gavinbreaux777/Cam_Tracking_Pi/not_code/Images/Physical_System/Belt_Driven_Pan_Table_Img3.jpg

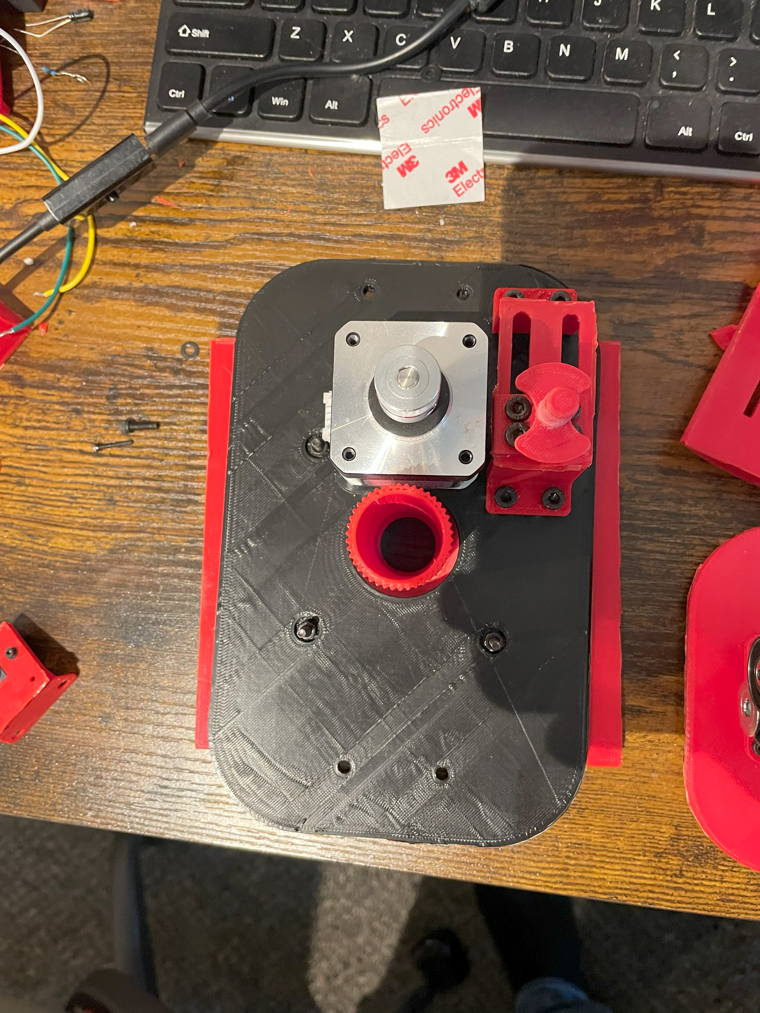
not_code/Images/Physical_System/Belt_Driven_Pan_Table_Img3.jpg
