gavinbreaux777/Cam_Tracking_Pi/not_code/Solidworks/V4_X Motor Tensioner Mount_V4.SLDPRT

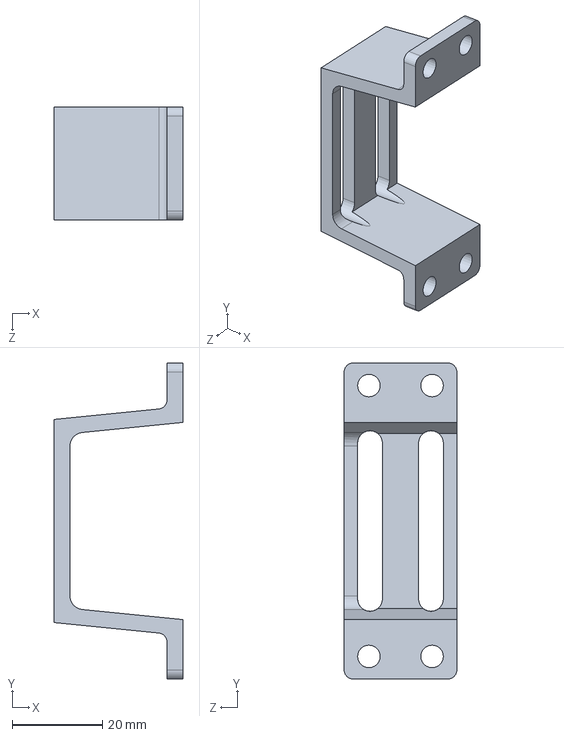
[picture p17: CAD file, 2026-02-15]
not_code/Solidworks/V4_X Motor Tensioner Mount_V4.SLDPRT
28.5 x 70.0 x 25.0 mm
