gavinbreaux777/Cam_Tracking_Pi/not_code/Solidworks/V4_SD Card Slot, RPi4ModelB.SLDPRT

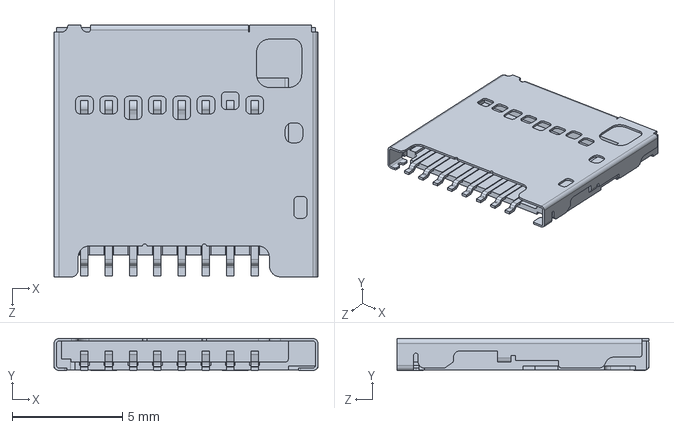
[picture p18: CAD file, 2026-02-15]
not_code/Solidworks/V4_SD Card Slot, RPi4ModelB.SLDPRT
11.9 x 1.45 x 11.4 mm
