gavinbreaux777/Cam_Tracking_Pi/not_code/Solidworks/V4_Cam case V4.SLDPRT

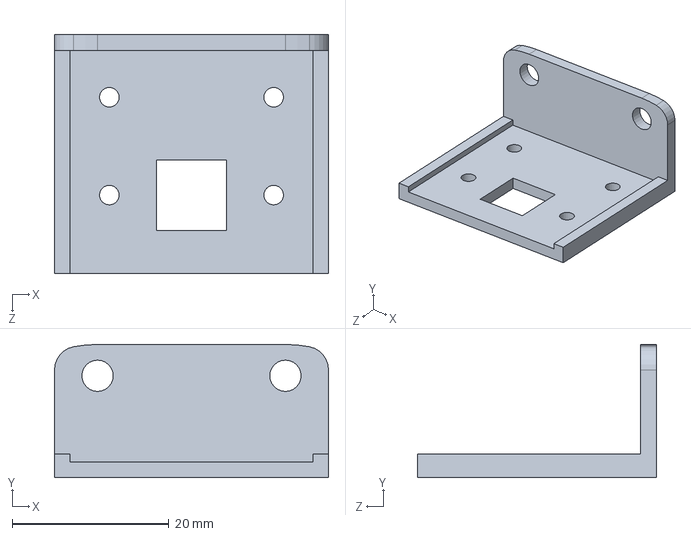
[picture p19: CAD file, 2026-02-15]
not_code/Solidworks/V4_Cam case V4.SLDPRT
35.0 x 17.0 x 30.5 mm
