gavinbreaux777/Cam_Tracking_Pi/not_code/Solidworks/V4_X Motor Tensioner Rod Cap.SLDPRT

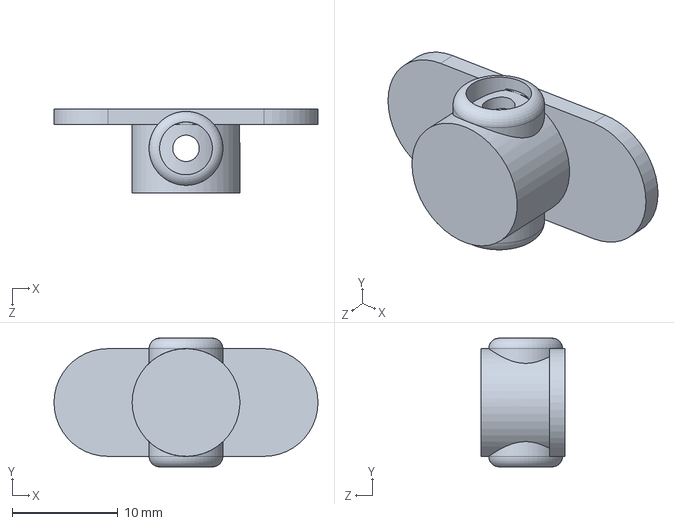
[picture p20: CAD file, 2026-02-15]
not_code/Solidworks/V4_X Motor Tensioner Rod Cap.SLDPRT
25.0 x 12.2 x 8.00 mm
