gavinbreaux777/Cam_Tracking_Pi/not_code/Solidworks/V4_Servo gate attachment.SLDPRT

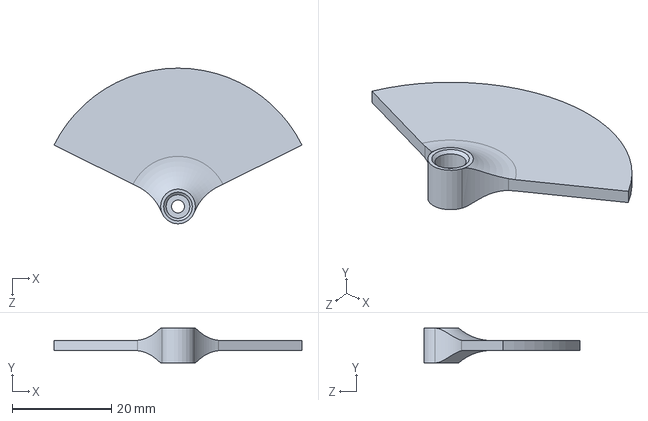
[picture p21: CAD file, 2026-02-15]
not_code/Solidworks/V4_Servo gate attachment.SLDPRT
50.0 x 7.00 x 31.4 mm
