gavinbreaux777/Cam_Tracking_Pi/not_code/Solidworks/V4_Direct Motor Mount V6_V3.SLDPRT

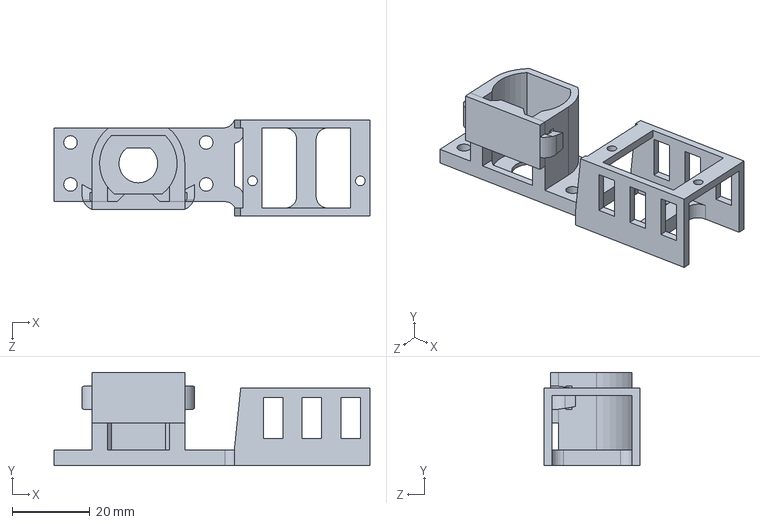
[picture p22: CAD file, 2026-02-15]
not_code/Solidworks/V4_Direct Motor Mount V6_V3.SLDPRT
81.5 x 24.0 x 24.7 mm
