gavinbreaux777/Cam_Tracking_Pi/not_code/Solidworks/V4_Female USB Type C Connector, RPi4ModelB.SLDPRT

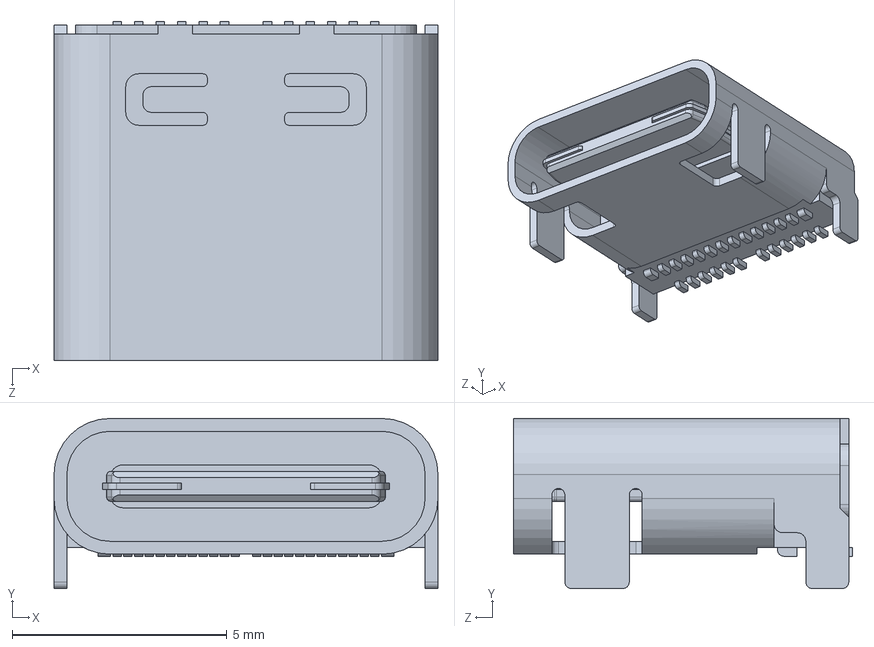
[picture p23: CAD file, 2026-02-15]
not_code/Solidworks/V4_Female USB Type C Connector, RPi4ModelB.SLDPRT
8.94 x 3.96 x 7.90 mm
