gavinbreaux777/Cam_Tracking_Pi/not_code/Solidworks/V4_Base_V3.SLDPRT

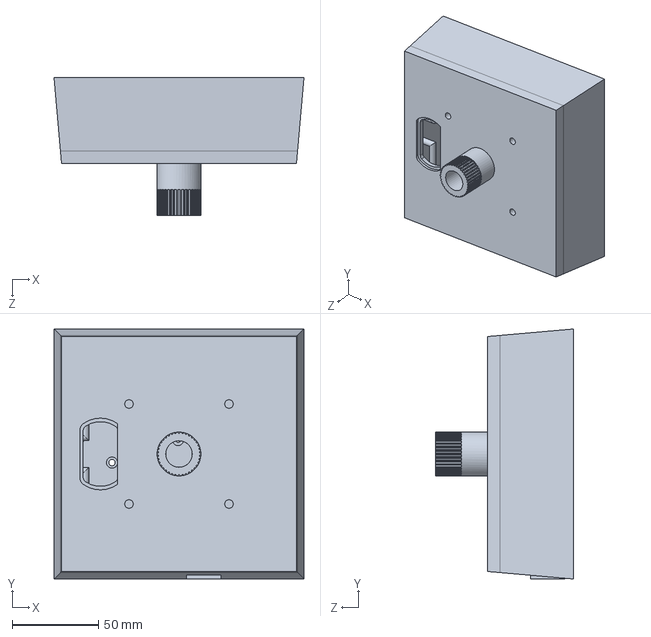
[picture p24: CAD file, 2026-02-15]
not_code/Solidworks/V4_Base_V3.SLDPRT
145.0 x 145.0 x 80.0 mm
