gavinbreaux777/Cam_Tracking_Pi/not_code/Solidworks/V4_Y Motor Tensioner Rod_V3.SLDPRT

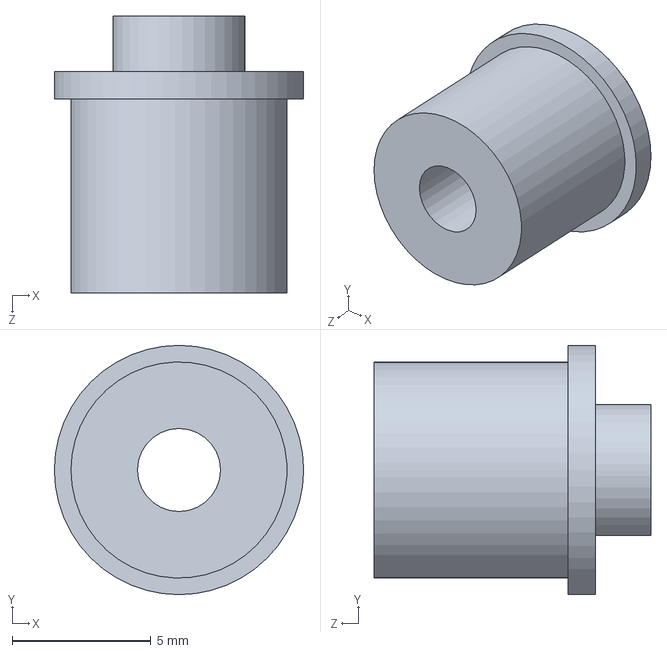
[picture p25: CAD file, 2026-02-15]
not_code/Solidworks/V4_Y Motor Tensioner Rod_V3.SLDPRT
9.00 x 9.00 x 10.0 mm
