gavinbreaux777/Cam_Tracking_Pi/not_code/Solidworks/V4_PCB, RPi4ModelB.SLDPRT

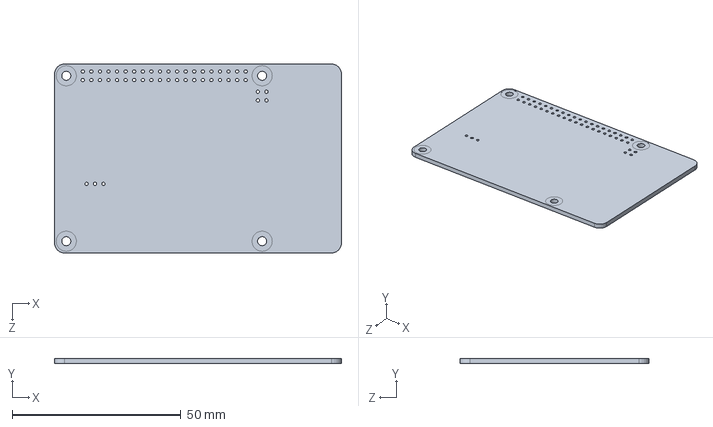
[picture p26: CAD file, 2026-02-15]
not_code/Solidworks/V4_PCB, RPi4ModelB.SLDPRT
85.0 x 1.60 x 56.0 mm
