gavinbreaux777/Cam_Tracking_Pi/not_code/Solidworks/V4_Gigabit Ethernet Port, RPi4ModelB.SLDPRT

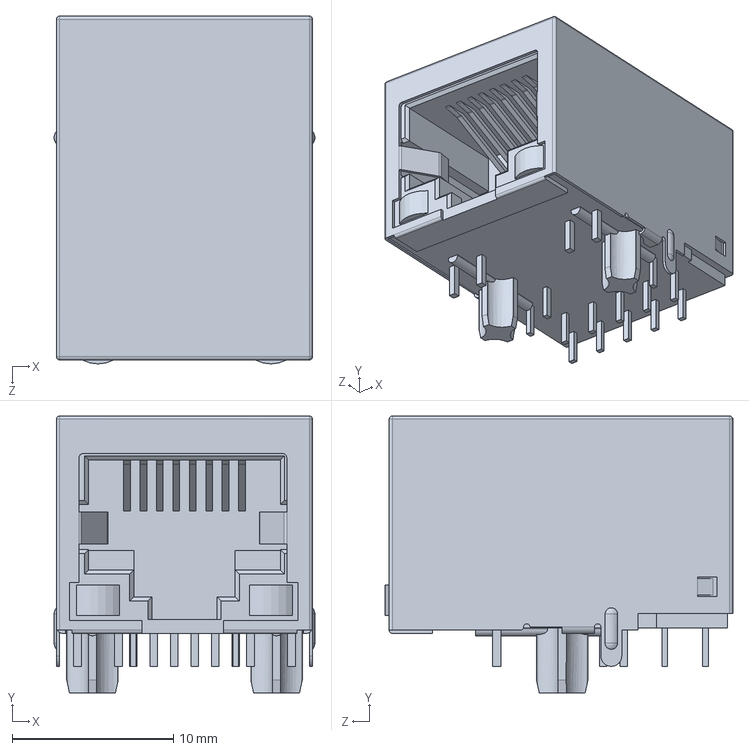
[picture p27: CAD file, 2026-02-15]
not_code/Solidworks/V4_Gigabit Ethernet Port, RPi4ModelB.SLDPRT
16.2 x 17.2 x 21.6 mm
