gavinbreaux777/Cam_Tracking_Pi/not_code/Solidworks/V4_Display Connector, RPi4ModelB.SLDPRT

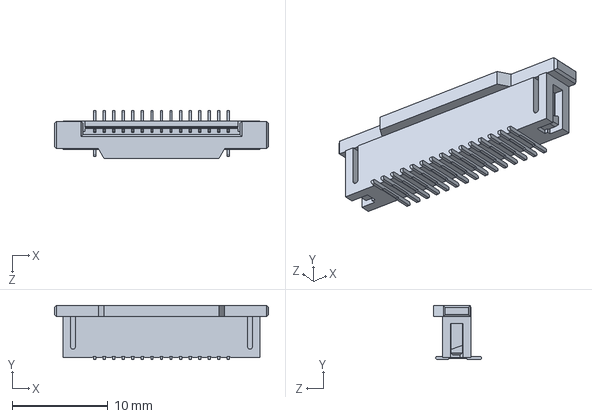
[picture p28: CAD file, 2026-02-15]
not_code/Solidworks/V4_Display Connector, RPi4ModelB.SLDPRT
22.4 x 5.68 x 5.07 mm
