gavinbreaux777/Cam_Tracking_Pi/not_code/Solidworks/V4 X Motor Upside Down Mount_1.SLDPRT

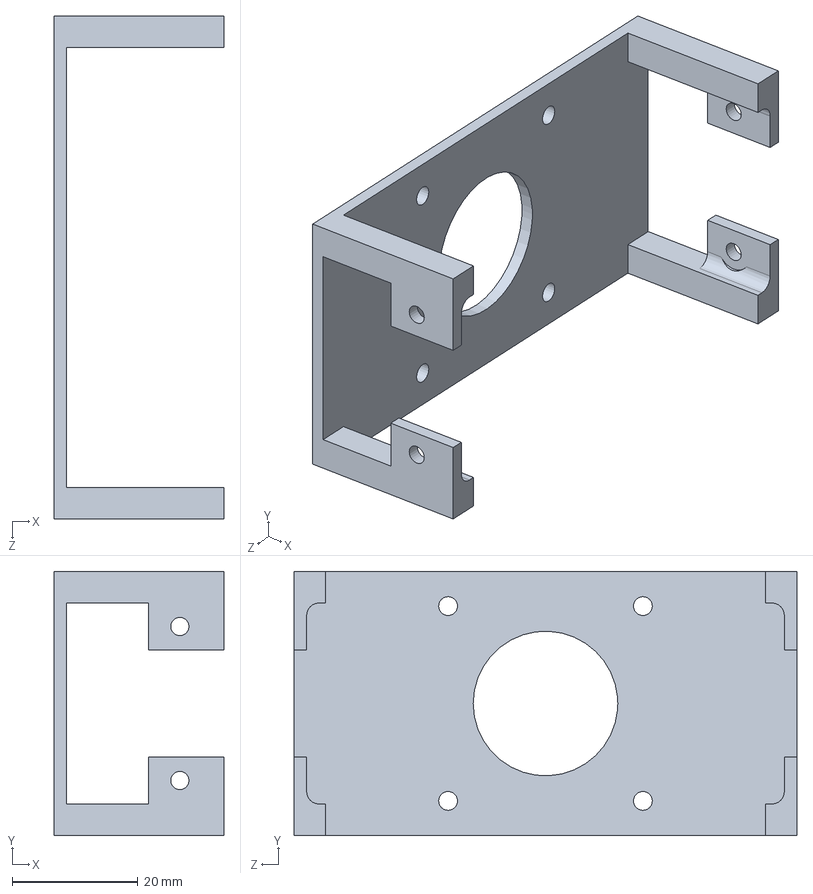
[picture p29: CAD file, 2026-02-15]
not_code/Solidworks/V4 X Motor Upside Down Mount_1.SLDPRT
27.0 x 42.0 x 80.0 mm
