gavinbreaux777/Cam_Tracking_Pi/not_code/Solidworks/V4_Ball Chute V3_V3.SLDPRT

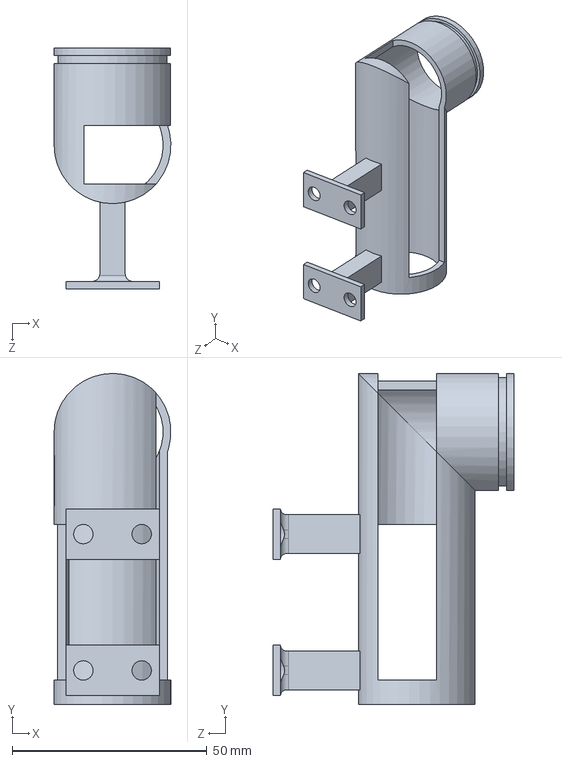
[picture p30: CAD file, 2026-02-15]
not_code/Solidworks/V4_Ball Chute V3_V3.SLDPRT
30.0 x 85.0 x 62.0 mm
