gavinbreaux777/Cam_Tracking_Pi/not_code/Solidworks/V4_Bearing Holder_1.SLDPRT

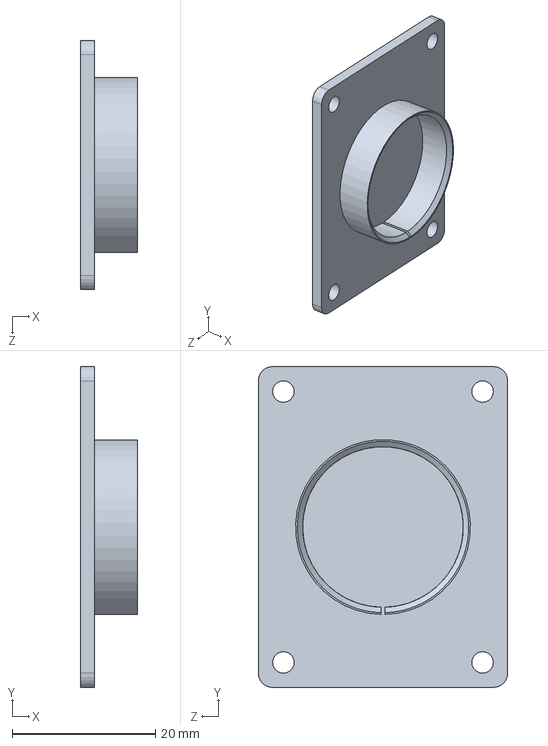
[picture p31: CAD file, 2026-02-15]
not_code/Solidworks/V4_Bearing Holder_1.SLDPRT
8.00 x 44.8 x 34.8 mm
