gavinbreaux777/Cam_Tracking_Pi/not_code/Solidworks/V4_2X USB3.0 PORTS, RPi4ModelB.SLDPRT

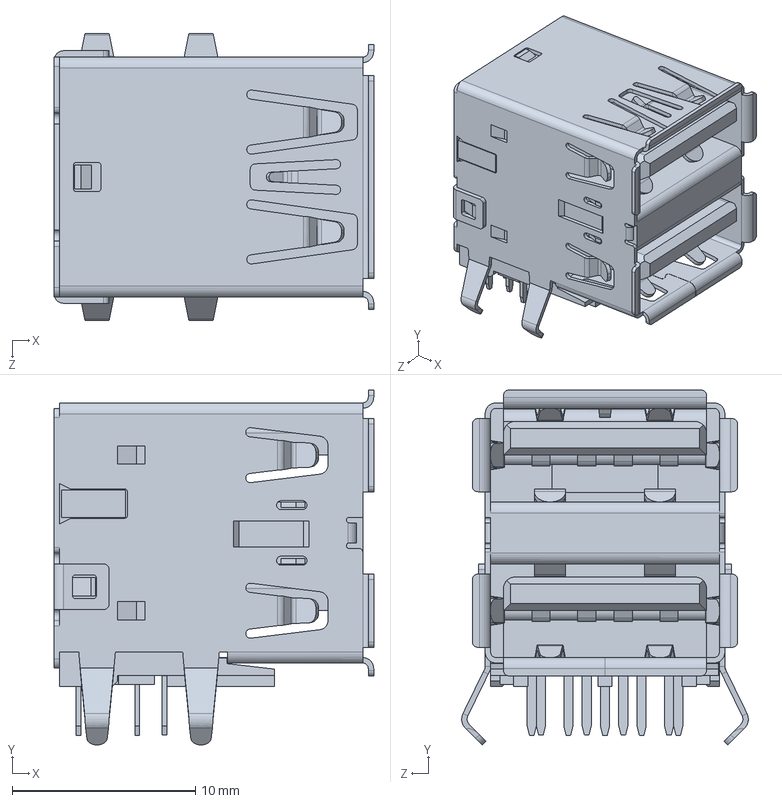
[picture p32: CAD file, 2026-02-15]
not_code/Solidworks/V4_2X USB3.0 PORTS, RPi4ModelB.SLDPRT
17.5 x 19.4 x 15.7 mm
