gavinbreaux777/Cam_Tracking_Pi/not_code/Solidworks/V4_Y Motor Shaft Gear Parametric.SLDPRT

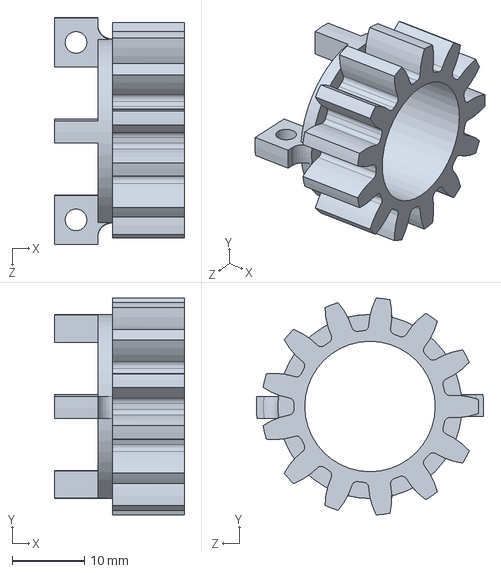
[picture p33: CAD file, 2026-02-15]
not_code/Solidworks/V4_Y Motor Shaft Gear Parametric.SLDPRT
18.0 x 30.0 x 31.4 mm
