gavinbreaux777/Cam_Tracking_Pi/not_code/Solidworks/V4_Half Lazy Susan_V3.SLDPRT

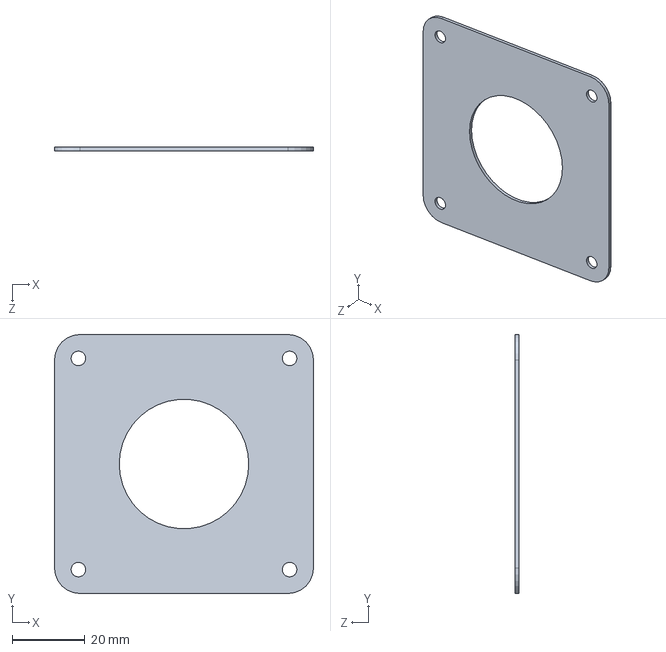
[picture p34: CAD file, 2026-02-15]
not_code/Solidworks/V4_Half Lazy Susan_V3.SLDPRT
71.1 x 71.1 x 1.00 mm
