gavinbreaux777/Cam_Tracking_Pi/not_code/Solidworks/V4_Female Micro HDMI Connector, RPi4ModelB.SLDPRT

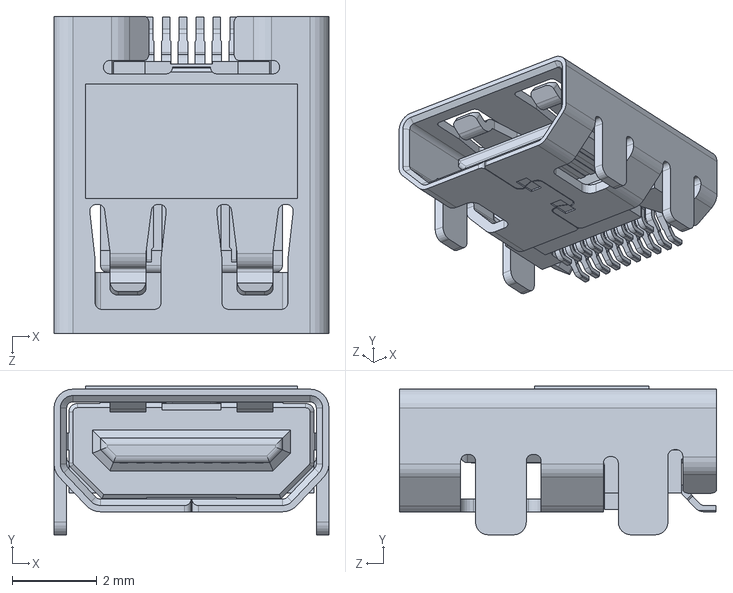
[picture p35: CAD file, 2026-02-15]
not_code/Solidworks/V4_Female Micro HDMI Connector, RPi4ModelB.SLDPRT
6.50 x 3.52 x 7.50 mm
