gavinbreaux777/Cam_Tracking_Pi/not_code/Solidworks/V4_Y Motor Shaft Gear Try 2.SLDPRT

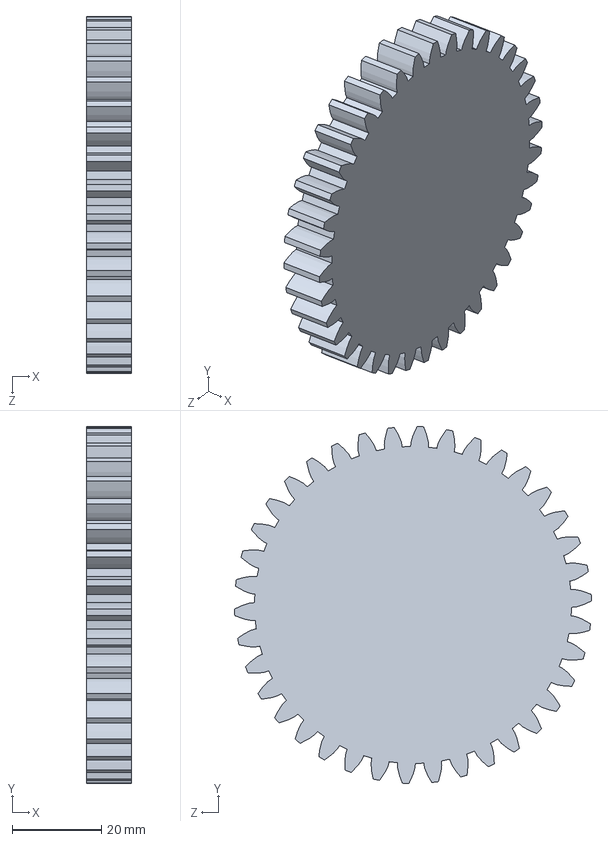
[picture p36: CAD file, 2026-02-15]
not_code/Solidworks/V4_Y Motor Shaft Gear Try 2.SLDPRT
10.0 x 80.0 x 80.0 mm
