gavinbreaux777/Cam_Tracking_Pi/not_code/Solidworks/V4_91D77 D9WHV 778K, 4 GB LPDDR4 SDRAM, RPi4ModelB.SLDPRT

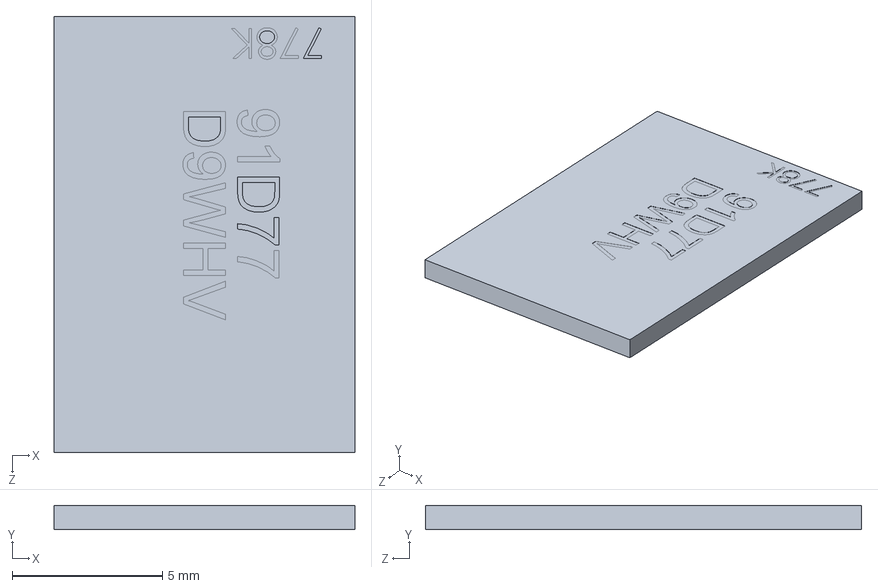
[picture p37: CAD file, 2026-02-15]
not_code/Solidworks/V4_91D77 D9WHV 778K, 4 GB LPDDR4 SDRAM, RPi4ModelB.SLDPRT
10.0 x 0.8 x 14.5 mm
