gavinbreaux777/Cam_Tracking_Pi/not_code/Solidworks/V4_Bearing_608_V3.SLDPRT

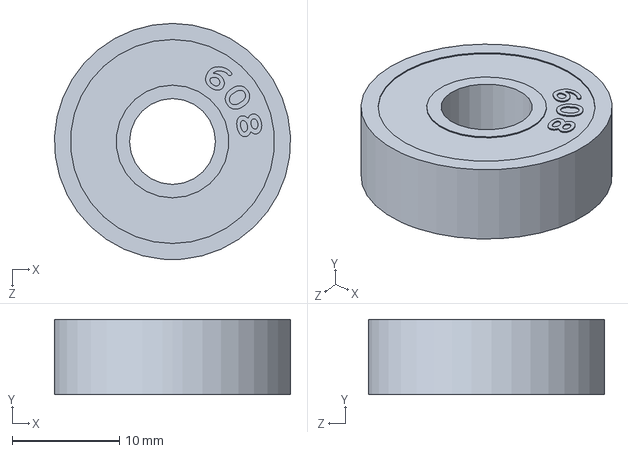
[picture p38: CAD file, 2026-02-15]
not_code/Solidworks/V4_Bearing_608_V3.SLDPRT
22.0 x 7.00 x 22.0 mm
