gavinbreaux777/Cam_Tracking_Pi/not_code/Solidworks/V4_2.54 mm DUPONT MALE PIN HEADER, IO, 2X20, RPi4ModelB.SLDPRT

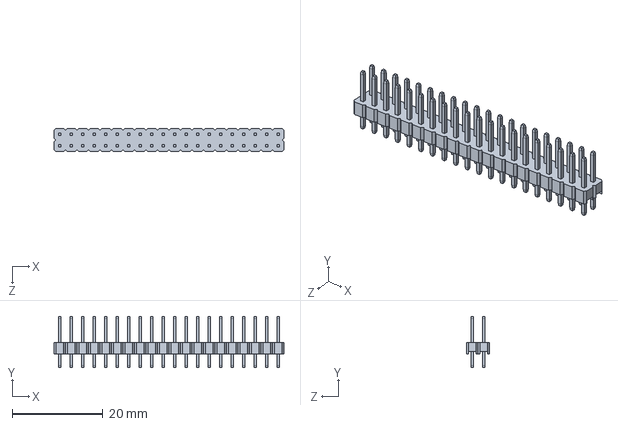
[picture p39: CAD file, 2026-02-15]
not_code/Solidworks/V4_2.54 mm DUPONT MALE PIN HEADER, IO, 2X20, RPi4ModelB.SLDPRT
50.8 x 11.3 x 5.08 mm
