gavinbreaux777/Cam_Tracking_Pi/not_code/Solidworks/V4_Cypress CYW43455 Wireless Module Cover, RPi4ModelB.SLDPRT

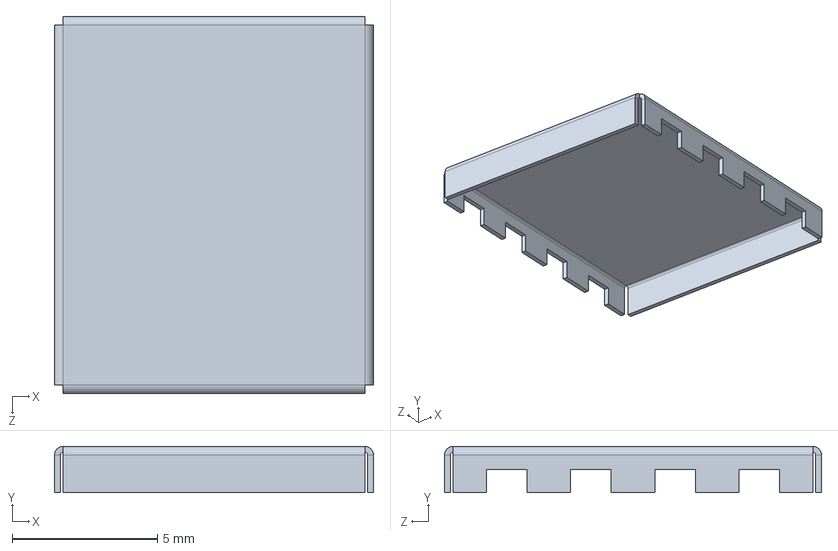
[picture p40: CAD file, 2026-02-15]
not_code/Solidworks/V4_Cypress CYW43455 Wireless Module Cover, RPi4ModelB.SLDPRT
11.0 x 1.60 x 13.0 mm
