gavinbreaux777/Cam_Tracking_Pi/not_code/Solidworks/V4_2X USB2.0 PORTS, RPi4ModelB.SLDPRT

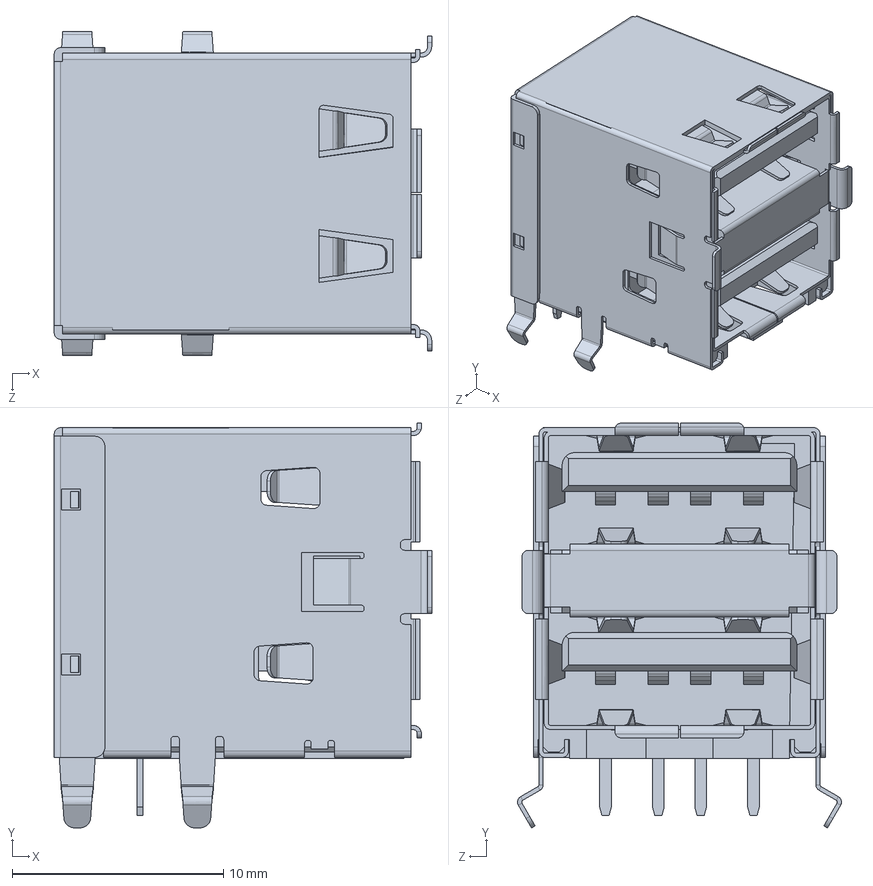
[picture p41: CAD file, 2026-02-15]
not_code/Solidworks/V4_2X USB2.0 PORTS, RPi4ModelB.SLDPRT
17.9 x 19.2 x 15.3 mm
