gavinbreaux777/Cam_Tracking_Pi/not_code/Solidworks/V4_MxL7704 Universal PMIC, RPi4ModelB.SLDPRT

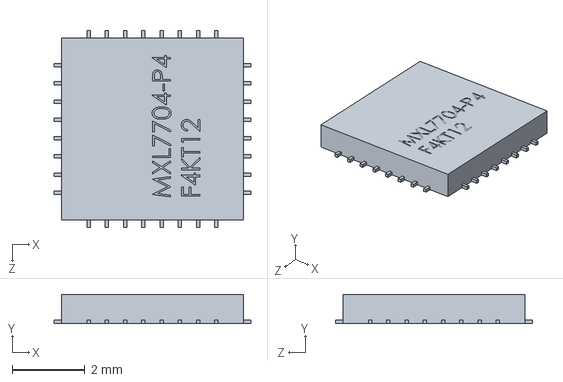
[picture p42: CAD file, 2026-02-15]
not_code/Solidworks/V4_MxL7704 Universal PMIC, RPi4ModelB.SLDPRT
5.40 x 0.8 x 5.40 mm
