gavinbreaux777/Cam_Tracking_Pi/not_code/Solidworks/V4_2.54 mm DUPONT MALE PIN HEADER, POE, 2X2, RPi4ModelB.SLDPRT

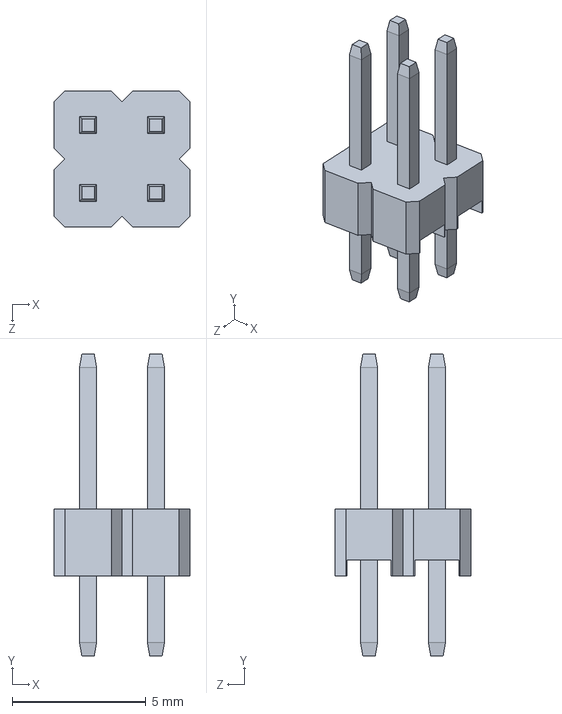
[picture p43: CAD file, 2026-02-15]
not_code/Solidworks/V4_2.54 mm DUPONT MALE PIN HEADER, POE, 2X2, RPi4ModelB.SLDPRT
5.08 x 11.3 x 5.08 mm
