gavinbreaux777/Cam_Tracking_Pi/not_code/Solidworks/V4_Raspberry Pi  Camera.SLDPRT

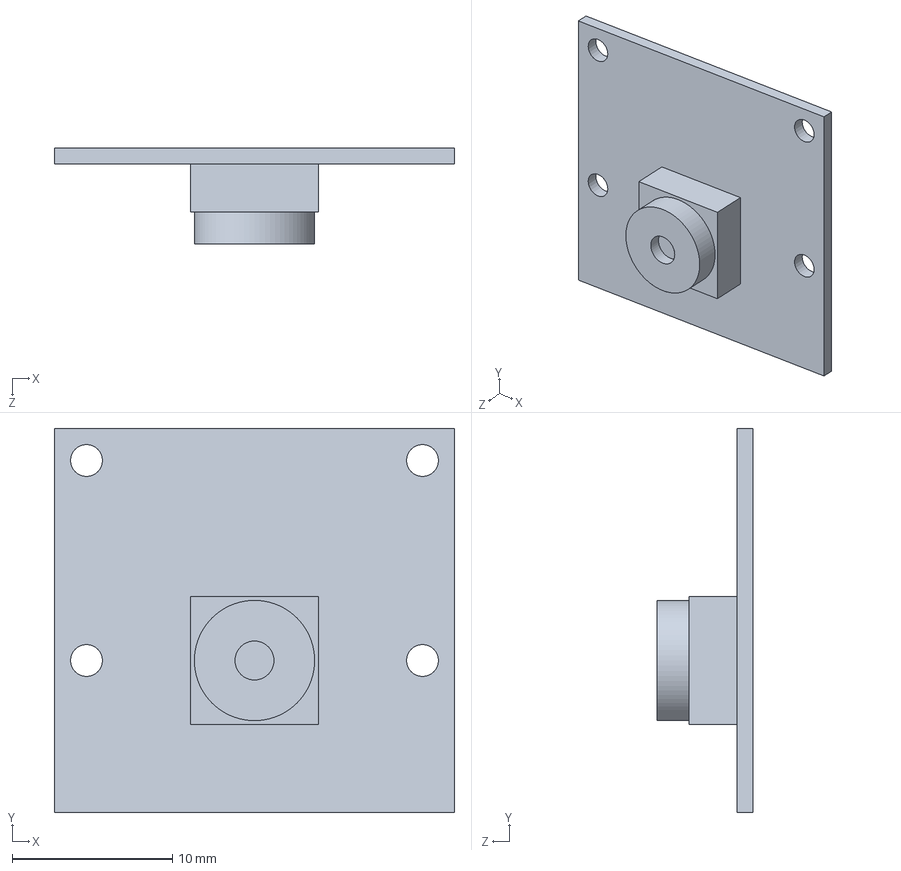
[picture p44: CAD file, 2026-02-15]
not_code/Solidworks/V4_Raspberry Pi Camera.SLDPRT
25.0 x 24.0 x 6.00 mm
