gavinbreaux777/Cam_Tracking_Pi/not_code/Solidworks/V4_Y Motor Shaft Gear Try 3.SLDPRT

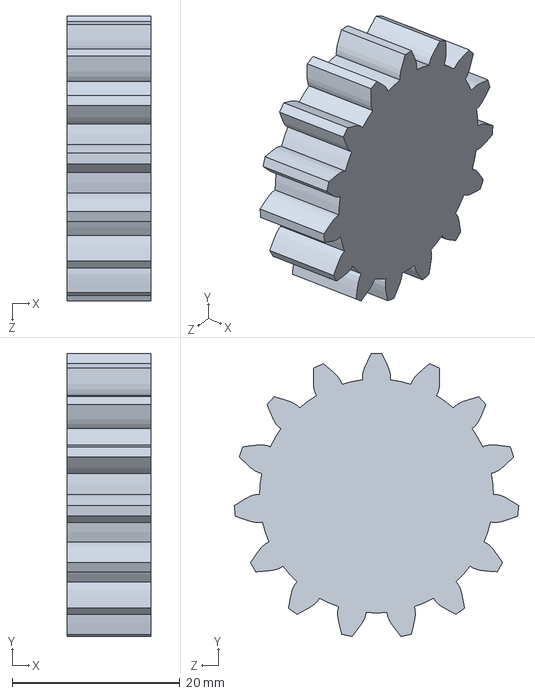
[picture p45: CAD file, 2026-02-15]
not_code/Solidworks/V4_Y Motor Shaft Gear Try 3.SLDPRT
10.0 x 33.7 x 33.9 mm
