gavinbreaux777/Cam_Tracking_Pi/not_code/Solidworks/V4_X Motor Tensioner Rod_V5.SLDPRT

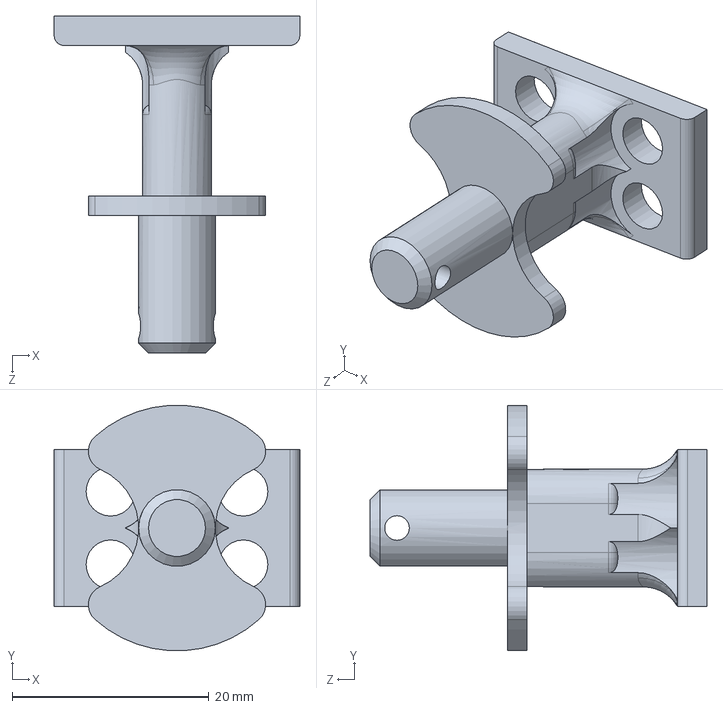
[picture p46: CAD file, 2026-02-15]
not_code/Solidworks/V4_X Motor Tensioner Rod_V5.SLDPRT
25.0 x 24.9 x 34.3 mm
