gavinbreaux777/Cam_Tracking_Pi/not_code/Solidworks/V4_Microphone Plug, RPi4ModelB.SLDPRT

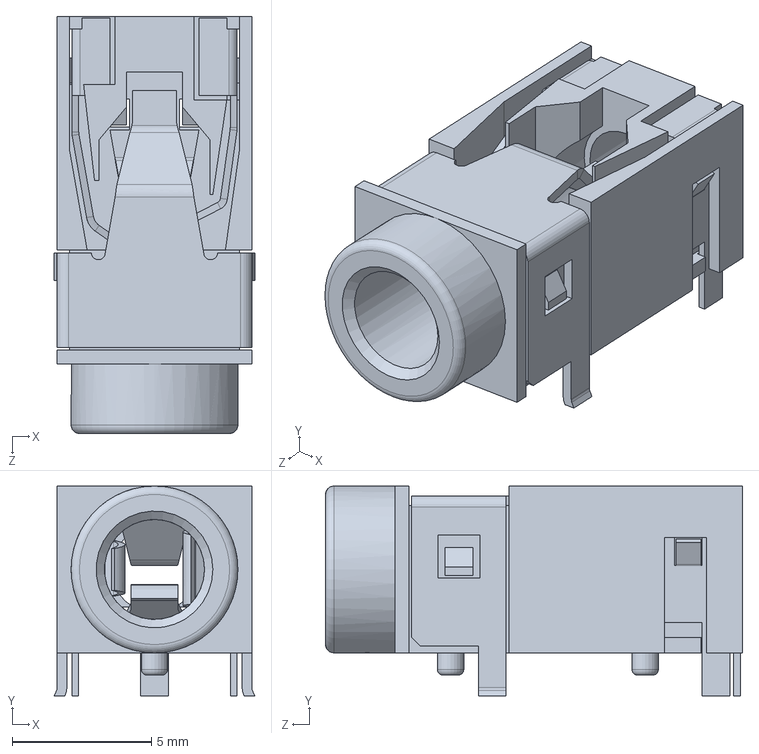
[picture p47: CAD file, 2026-02-15]
not_code/Solidworks/V4_Microphone Plug, RPi4ModelB.SLDPRT
7.23 x 7.55 x 15.0 mm
