gavinbreaux777/Cam_Tracking_Pi/not_code/Solidworks/V4_Base_V4.SLDPRT

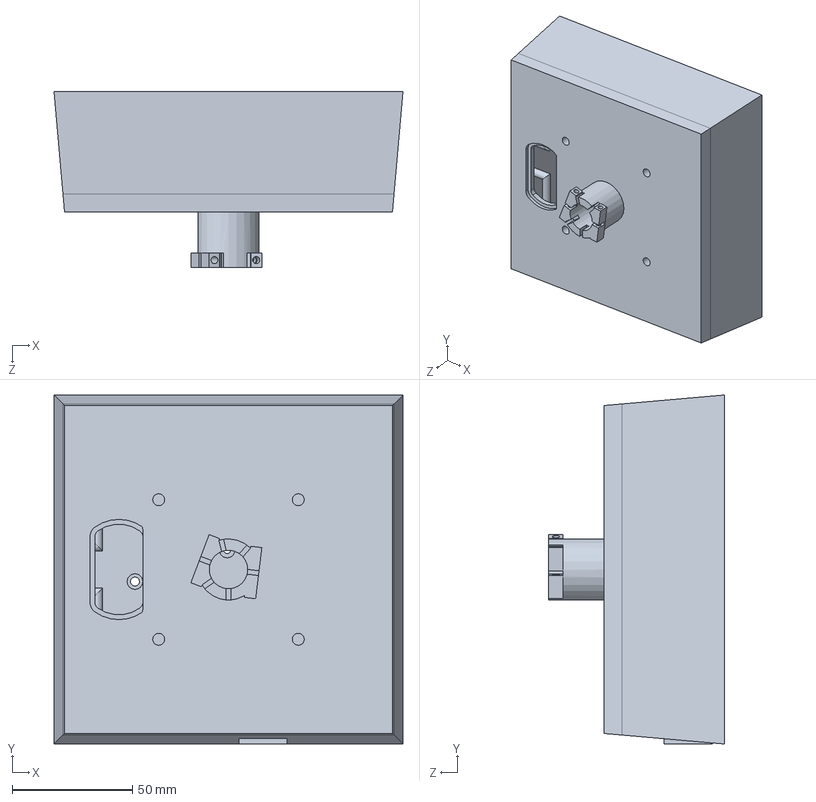
[picture p48: CAD file, 2026-02-15]
not_code/Solidworks/V4_Base_V4.SLDPRT
145.0 x 145.0 x 73.0 mm
