gavinbreaux777/Cam_Tracking_Pi/not_code/Solidworks/V4_Base_V5SLDPRT.SLDPRT

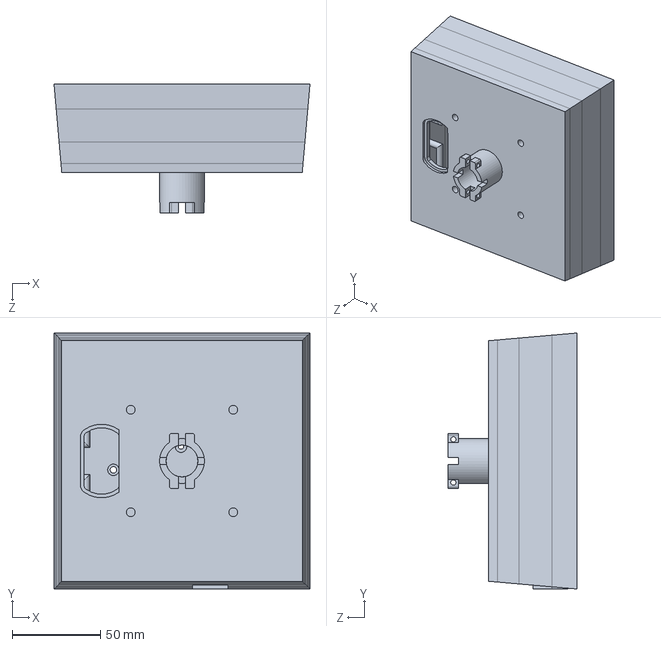
[picture p49: CAD file, 2026-02-15]
not_code/Solidworks/V4_Base_V5SLDPRT.SLDPRT
145.0 x 145.0 x 73.0 mm
