gavinbreaux777/Cam_Tracking_Pi/not_code/Solidworks/V4_Tilt Table Riser_Adjustable_Bearing_1.SLDPRT

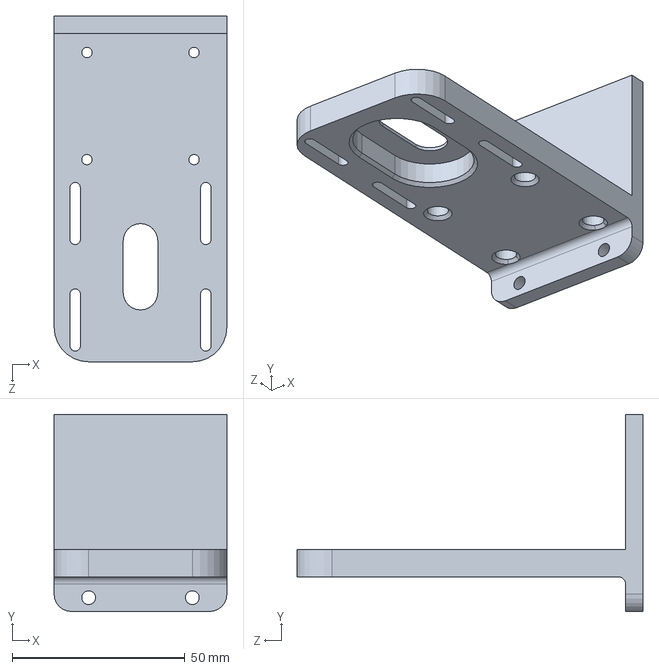
[picture p50: CAD file, 2026-02-15]
not_code/Solidworks/V4_Tilt Table Riser_Adjustable_Bearing_1.SLDPRT
50.0 x 57.0 x 100.0 mm
