gavinbreaux777/Cam_Tracking_Pi/not_code/Solidworks/V4_Broadcom BCM2711B0 CPU, RPi4ModelB.SLDPRT

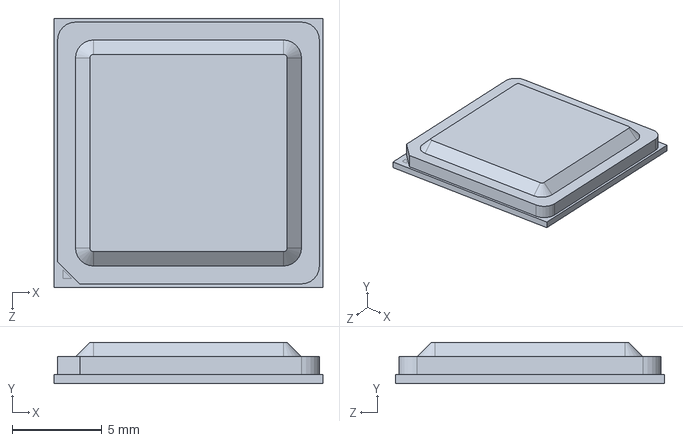
[picture p51: CAD file, 2026-02-15]
not_code/Solidworks/V4_Broadcom BCM2711B0 CPU, RPi4ModelB.SLDPRT
15.0 x 2.30 x 15.0 mm
