gavinbreaux777/Cam_Tracking_Pi/not_code/Solidworks/V4_Motor_130.SLDPRT

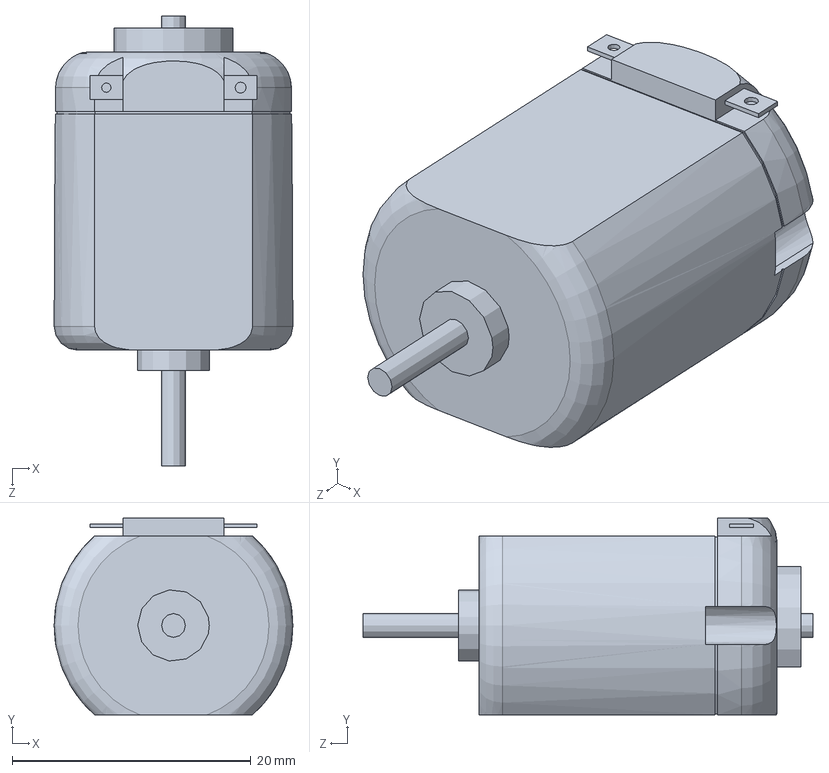
[picture p52: CAD file, 2026-02-15]
not_code/Solidworks/V4_Motor_130.SLDPRT
20.0 x 16.5 x 37.7 mm
