gavinbreaux777/Cam_Tracking_Pi/not_code/Solidworks/V4_3764N104_High-Strength Gt Timing Belt Pulley_V3.SLDPRT

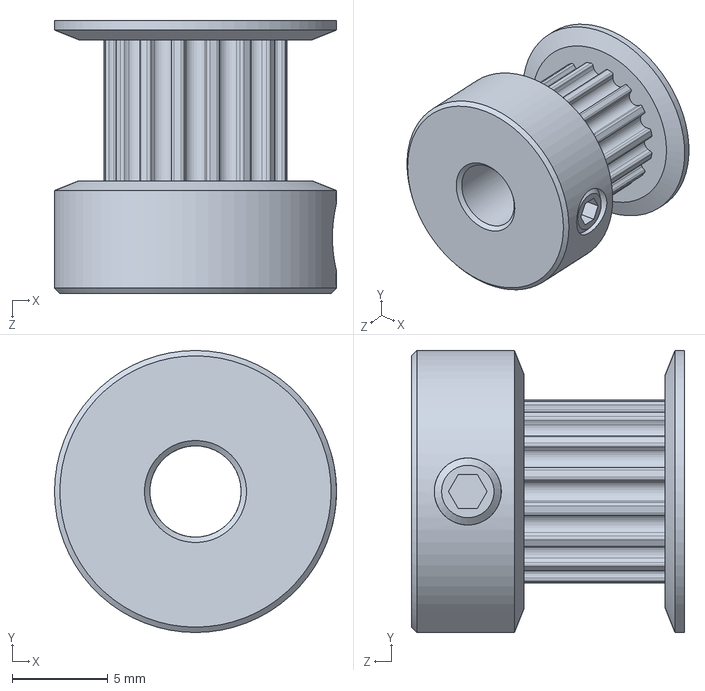
[picture p53: CAD file, 2026-02-15]
not_code/Solidworks/V4_3764N104_High-Strength Gt Timing Belt Pulley_V3.SLDPRT
14.7 x 14.7 x 14.3 mm
