gavinbreaux777/Cam_Tracking_Pi/not_code/Solidworks/V4_Tilt Table_V3.SLDPRT

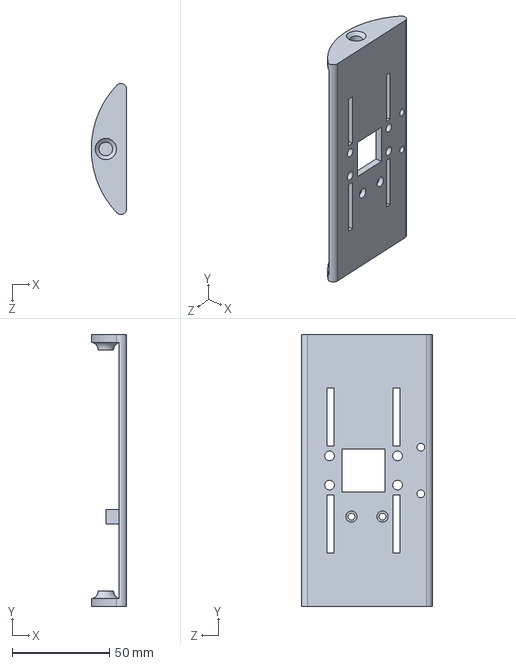
[picture p54: CAD file, 2026-02-15]
not_code/Solidworks/V4_Tilt Table_V3.SLDPRT
18.2 x 140.0 x 67.4 mm
