gavinbreaux777/Cam_Tracking_Pi/not_code/Solidworks/V4_Bearing to Tilt Table Shaft_V4.SLDPRT

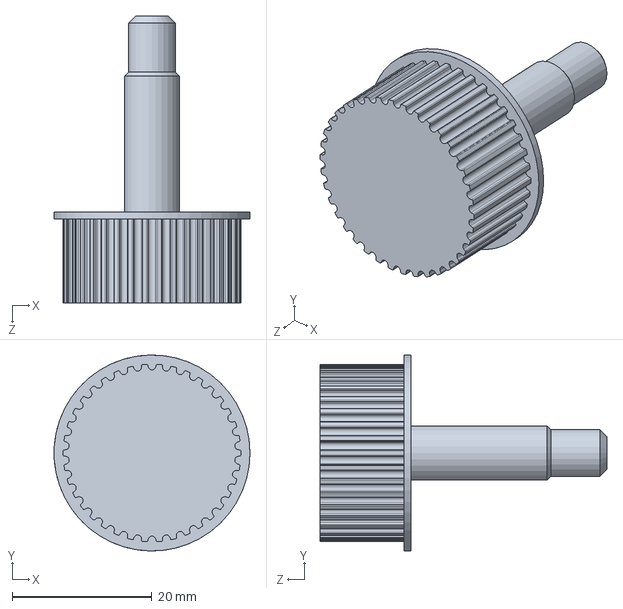
[picture p55: CAD file, 2026-02-15]
not_code/Solidworks/V4_Bearing to Tilt Table Shaft_V4.SLDPRT
28.0 x 28.0 x 41.0 mm
