gavinbreaux777/Cam_Tracking_Pi/not_code/Solidworks/V4_VIA VL805 PCIe USB 3.0 controller, RPi4ModelB.SLDPRT

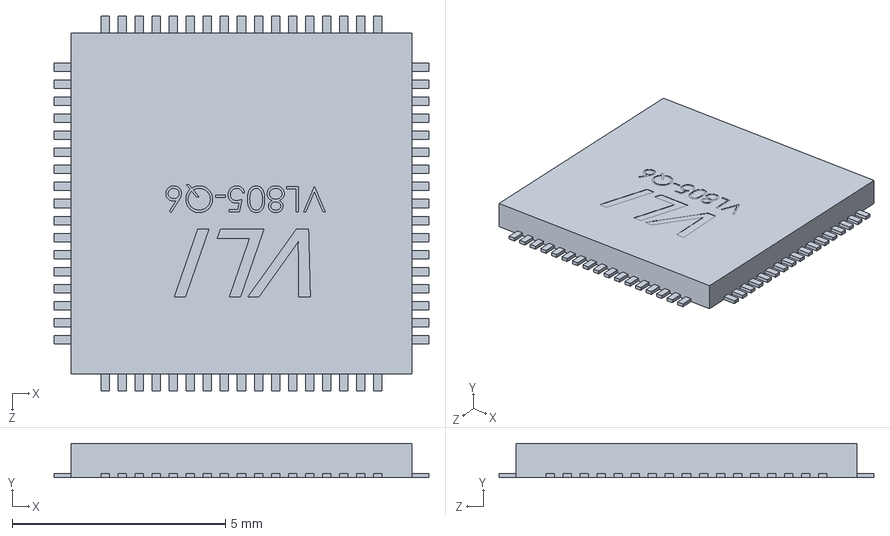
[picture p56: CAD file, 2026-02-15]
not_code/Solidworks/V4_VIA VL805 PCIe USB 3.0 controller, RPi4ModelB.SLDPRT
8.80 x 0.8 x 8.80 mm
