gavinbreaux777/Cam_Tracking_Pi/not_code/Solidworks/V4_Tilt Table Riser_V3.SLDPRT

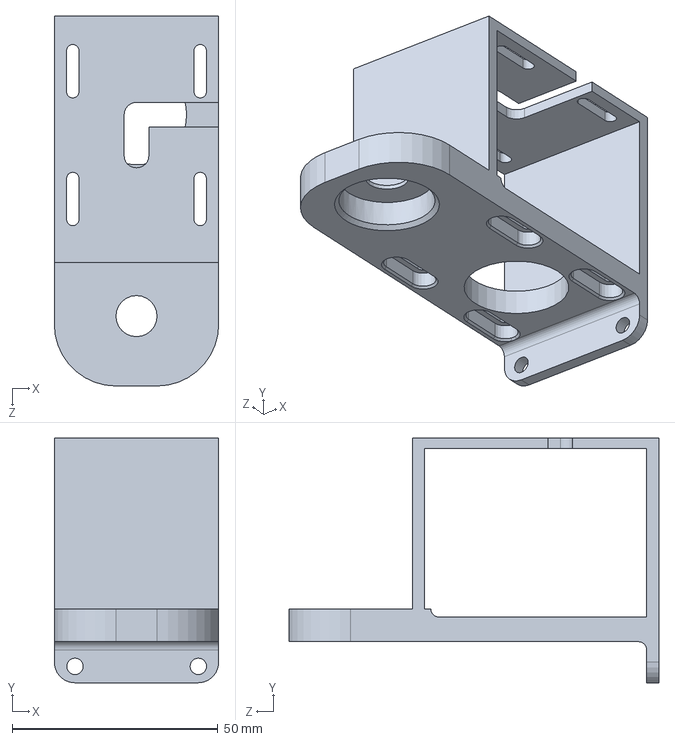
[picture p57: CAD file, 2026-02-15]
not_code/Solidworks/V4_Tilt Table Riser_V3.SLDPRT
40.0 x 59.5 x 90.0 mm
