gavinbreaux777/Cam_Tracking_Pi/not_code/Solidworks/V4_Motor Wheel V4.SLDPRT

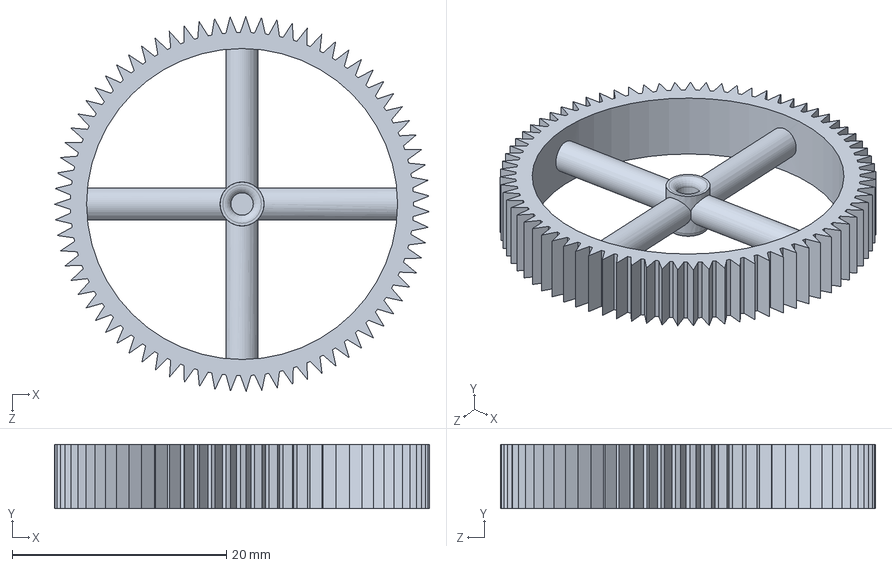
[picture p58: CAD file, 2026-02-15]
not_code/Solidworks/V4_Motor Wheel V4.SLDPRT
35.0 x 6.00 x 35.0 mm
