gavinbreaux777/Cam_Tracking_Pi/not_code/Solidworks/V4_Y Motor Tensioner Mount_V3.SLDPRT

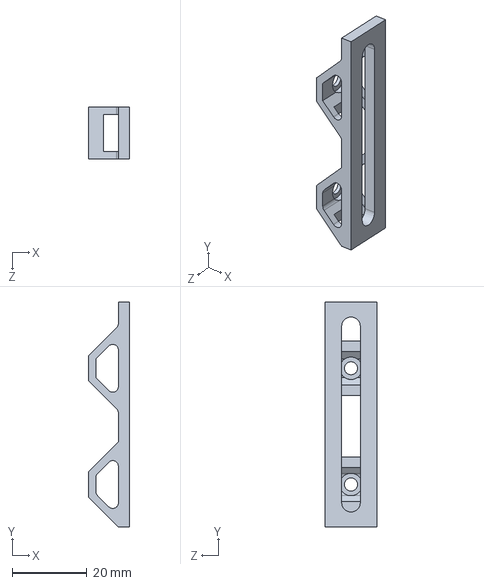
[picture p59: CAD file, 2026-02-15]
not_code/Solidworks/V4_Y Motor Tensioner Mount_V3.SLDPRT
11.0 x 60.0 x 14.0 mm
