gavinbreaux777/Cam_Tracking_Pi/not_code/Solidworks/V4_Broadcom BCM54213PE Gigabit Ethernet Transceiver, RPi4ModelB.SLDPRT

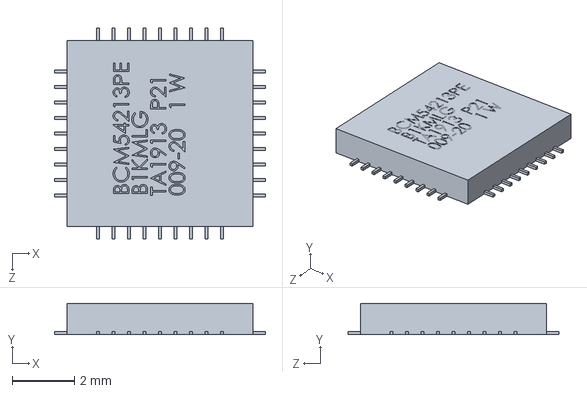
[picture p60: CAD file, 2026-02-15]
not_code/Solidworks/V4_Broadcom BCM54213PE Gigabit Ethernet Transceiver, RPi4ModelB.SLDPRT
6.80 x 1.00 x 6.80 mm
