gavinbreaux777/Cam_Tracking_Pi/not_code/Images/CAD/V4/Main_Assembly_Img1.PNG

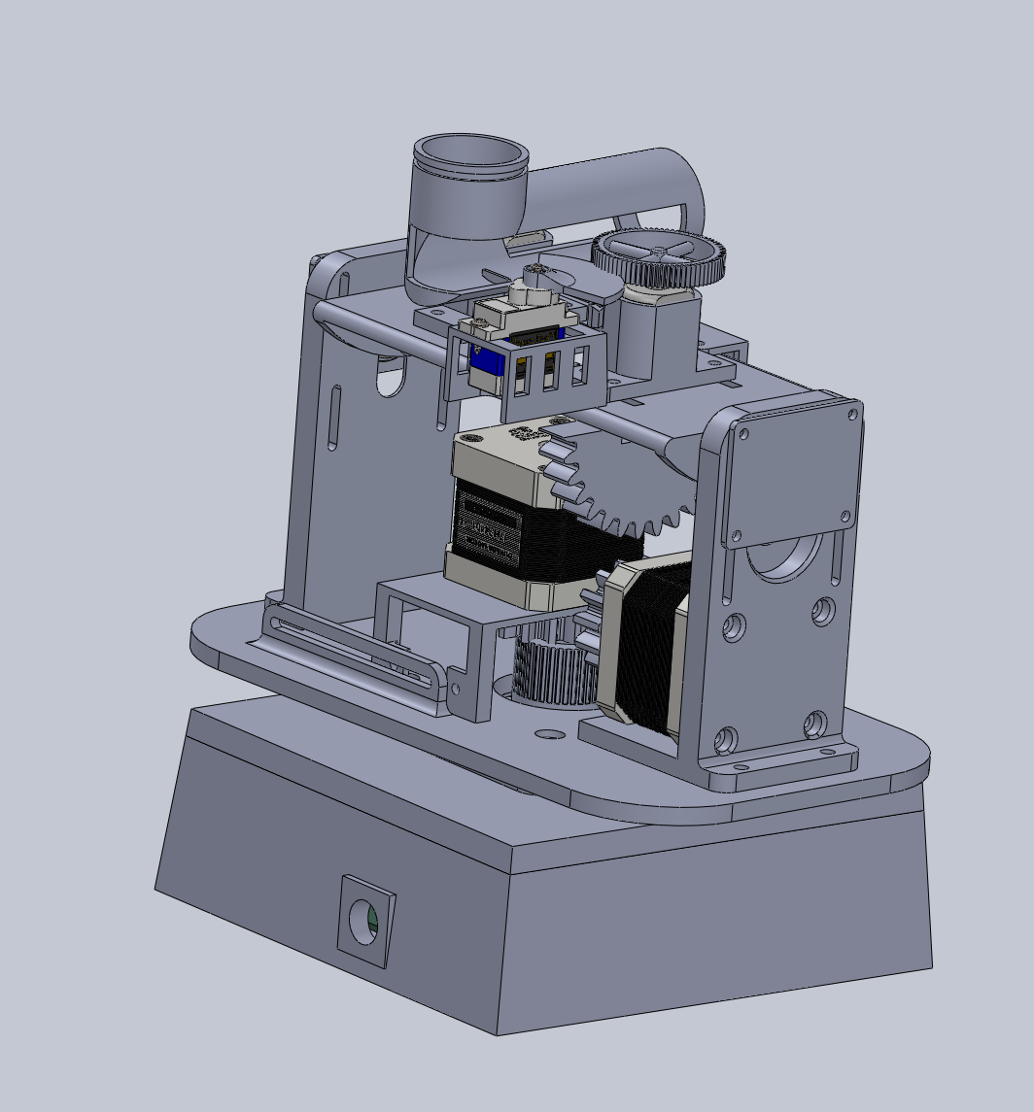
not_code/Images/CAD/V4/Main_Assembly_Img1.PNG
