gavinbreaux777/Cam_Tracking_Pi/motors/RawServoControl.py

from i_o.IOControl import IOControl
from config.ConfigClasses import ChamberServoConfig

class RawServoControl():
    def __init__(self, ioControl: IOControl, config: ChamberServoConfig):
        self.ioControl = ioControl
        self._pwmPin = config.pwmPin
        self._minAngle = 0
        self._maxAngle = 180
        self._minDutyCycle = 500
        self._maxDutyCycle = 2500
        self._dutyCyclePerDegree = (self._maxDutyCycle - self._minDutyCycle) / (self._maxAngle - self._minAngle)

        self.ioControl.SetPinMode(self._pwmPin, 1)
        self.ioControl.SetPWMFrequency(self._pwmPin, config.pulseFrequency)
        self.SetAngle(self._minAngle)

    def SetAngle(self, angle: float):
        if(angle < self._minAngle or angle > self._maxAngle):
            print(f"Angle out of range. Range = {self._minAngle} - {self._maxAngle}")
            return
        dutyCycle = int(500 + (angle * self._dutyCyclePerDegree))
        self.ioControl.SetPWMDutyCycle(self._pwmPin, dutyCycle)
        self.position = angle
