gavinbreaux777/Cam_Tracking_Pi/ClassFactory.py

from config.AppConfig import *
from unittest.mock import MagicMock
import time

class ClassFactory():
    def __init__(self):
        pass

    @staticmethod
    def ReturnCamera(config: CameraConfig):        
        from camera.CameraInterface import CameraInterface
        if(config.mock):
            import numpy as np
            mock_camera = MagicMock()

            def fake_capture():
                time.sleep(0.01)
                return np.zeros((480, 640, 3), dtype=np.uint8)
            mock_camera.Picamera2.capture_array.side_effect = fake_capture            
            
            return mock_camera
        
        else:
            import picamera2
            picamFromLib = picamera2
            cameraInterfacePicam = CameraInterface()
            cameraInterfacePicam.Picamera2 = picamFromLib.Picamera2()
            cameraInterfacePicam.encoders = picamera2.encoders
            cameraInterfacePicam.outputs = picamera2.outputs
            cameraInterfacePicam.Picamera2.MappedArray = picamFromLib.MappedArray
            cameraInterfacePicam.imgSize = config.imgSize
            return cameraInterfacePicam

    @staticmethod
    def ReturnIO(config: IOConfig):
        if(config.mock):
            return MagicMock()
        else:
            import pigpio
            return pigpio.pi()
        
    @staticmethod
    def ReturnMotorControl(ioControl, motorConfig: MotorConfig, systemConfig: SystemConfig):
        from motors.MotorControl import MotorControl
        from motors.AimingControl import AimingControl
        from motors.DCMotorControl import DCMotorControl
        from motors.RawServoControl import RawServoControl
        from motors.stepper_control.StepperMotorControl import StepperMotorControl
        from motors.FiringControl import FiringControl
        from motors.AmmoControl import AmmoControl

        #initialize individual motor classes and then pass to MotorControl
        panMotor = StepperMotorControl(ioControl, motorConfig.aimMotors.panMotor)
        tiltMotor = StepperMotorControl(ioControl, motorConfig.aimMotors.tiltMotor)
        aimingControl = AimingControl(panMotor, tiltMotor)

        chamberServo = RawServoControl(ioControl, motorConfig.chamberServo)
        ammoControl = AmmoControl(chamberServo, motorConfig.chamberServo)
        spoolMotors = DCMotorControl(ioControl, motorConfig.firingMotor)
        firingControl = FiringControl(ammoControl, spoolMotors, systemConfig)

        motorControl = MotorControl(aimingControl, firingControl, systemConfig)
        return motorControl

        if(motorConfig.aimMotors.panMotor.mock or
           motorConfig.aimMotors.tiltMotor.mock or 
           motorConfig.firingMotor.mock or 
           motorConfig.chamberServo.mock):
            raise Exception("Individual motor mocking not supported yet - use IO mocking instead to mock all motors")
        else:
            return MotorControl(ioControl, motorConfig)
